LenweSaralonde/pico-midi-merger/pico-midi-merger.kicad_sch

## KiCad design pico-midi-merger.kicad_sch (2023-08-06)

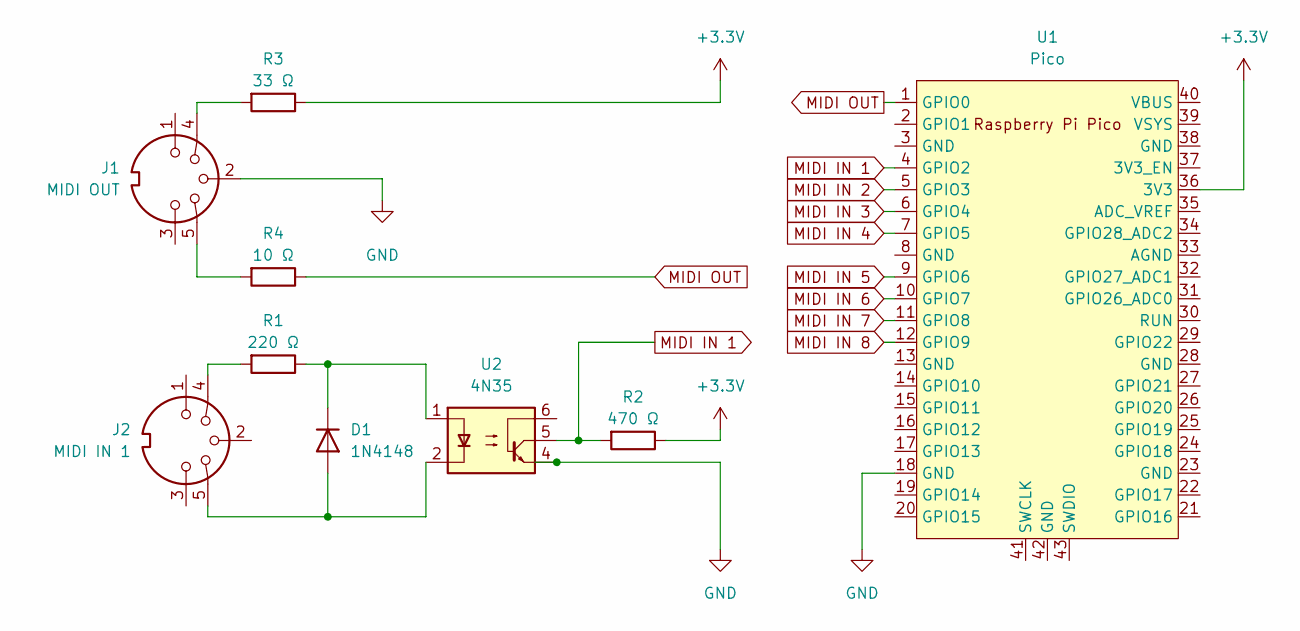
[picture p3: schematic pico-midi-merger.kicad_sch]

Parts:
D1: 1N4148; D_DO-35_SOD27_P7.62mm_Horizontal
J1: MIDI OUT
J2: MIDI IN 1
R1: 220 Ω
R2: 470 Ω
R3: 33 Ω
R4: 10 Ω
U1: Pico; RPi_Pico_SMD_TH
U2: 4N35; DIP-6_W7.62mm

Connections:
+3.3V: R2.1, R3.1, U1.36 (3V3)
GND: J1.2, U1.18 (GND), U2.4
MIDI IN 1: R2.2, U1.4 (GPIO2), U2.5
MIDI IN 2: U1.5 (GPIO3)
MIDI IN 3: U1.6 (GPIO4)
MIDI IN 4: U1.7 (GPIO5)
MIDI IN 5: U1.9 (GPIO6)
MIDI IN 6: U1.10 (GPIO7)
MIDI IN 7: U1.11 (GPIO8)
MIDI IN 8: U1.12 (GPIO9)
MIDI OUT: R4.1, U1.1 (GPIO0)
unnamed: D1.1 (K), R1.1, U2.1
unnamed: D1.2 (A), J2.5, U2.2
unnamed: J1.4, R3.2
unnamed: J1.5, R4.2
unnamed: J2.4, R1.2
